tomcombriat/TES_8-knobs-synth/XORAND_sax_chord/midi_handles.h

#ifndef _midi_handles_
#define _midi_handles_

void HandleNoteOn(byte channel, byte note, byte velocity);
void HandleNoteOff(byte channel, byte note, byte velocity);
void HandleControlChange(byte channel, byte control, byte val);

#endif
